git-blu/midnyte/src/Display.cpp

#include "Display.hpp"

// Static initialization
DisplayDriver Display::displayDriver;
Pixel Display::pixel;

// -----------------------------------------------------------------------------
// Construction
// -----------------------------------------------------------------------------
Display::Display() {
}


// -----------------------------------------------------------------------------
// Public methods
// -----------------------------------------------------------------------------
void Display::Touch(const uint8_t x, const uint8_t y){
}


// -----------------------------------------------------------------------------
// Implementation
// -----------------------------------------------------------------------------
void Display::MainMenu() {
}
