git-blu/midnyte/src/mcu.h

#ifndef F_CPU
#define F_CPU 16000000UL
#endif

#ifndef __OPTIMIZE__
#define __OPTIMIZE__
#endif

#ifndef __AVR_ATmega32U4__
#define __AVR_ATmega32U4__
#endif

#include <avr/io.h>
#include <avr/interrupt.h>
#include <util/delay.h>
